NRG24/Cognitive-State-RIng/Flex Ring PCB and Schematic/Flex Ring.kicad_sch

## KiCad design Flex Ring PCB and Schematic/Flex Ring.kicad_sch (2025-12-12)

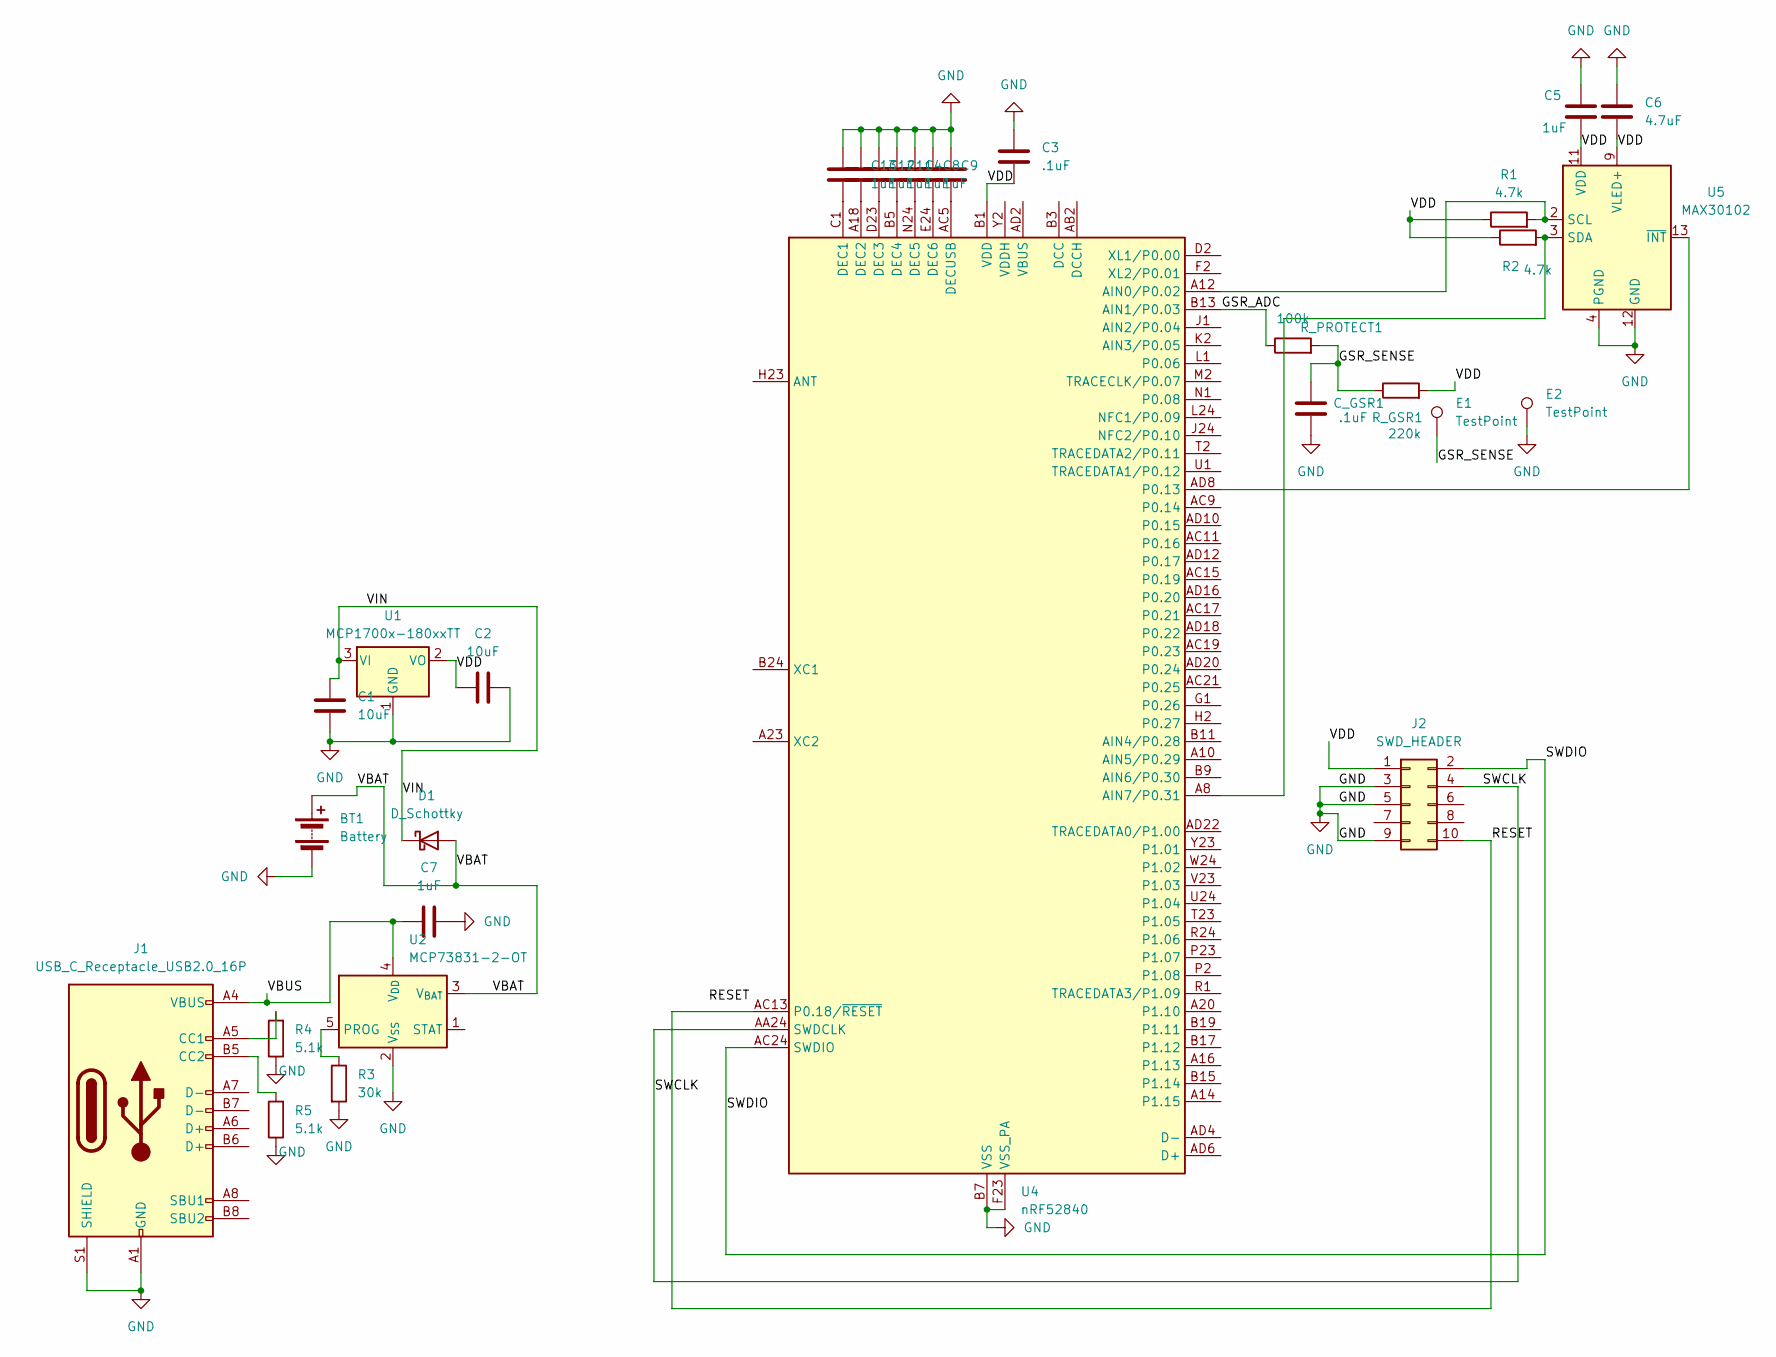
[picture p6: schematic Flex Ring.kicad_sch]

Parts:
BT1: Battery; SolderWire-0.127sqmm_1x02_P3.7mm_D0.48mm_OD1mm
C1, C2: 10uF; C_0603_1608Metric
C3: .1uF; C_0603_1608Metric
C4, C5, C7, C8, C9, C10, C11, C12, C13: 1uF; C_0603_1608Metric
C6: 4.7uF; C_0805_2012Metric
C_GSR1: .1uF; C_0603_1608Metric
D1: D_Schottky; D_SOD-123
E1: TestPoint; TestPoint_Pad_D2.0mm
E2: TestPoint; SolderWire-0.1sqmm_1x01_D0.4mm_OD1mm
J1: USB_C_Receptacle_USB2.0_16P; USB_C_Receptacle_HRO_TYPE-C-31-M-12
J2: SWD_HEADER; PinHeader_2x05_P1.27mm_Vertical
R1, R2: 4.7k; R_0603_1608Metric
R3: 30k; R_0603_1608Metric
R4, R5: 5.1k; R_0603_1608Metric
R_GSR1: 220k; R_0603_1608Metric
R_PROTECT1: 100k; R_0603_1608Metric
U1: MCP1700x-180xxTT; SOT-23
U2: MCP73831-2-OT; SOT-23-5
U4: nRF52840; Nordic_AQFN-73-1EP_7x7mm_P0.5mm
U5: MAX30102; Maxim_OLGA-14_3.3x5.6mm_P0.8mm

Connections:
GND: BT1.2 (-), C1.2, C2.2, C3.1, C4.1, C5.1, C6.1, C7.2, C8.1, C9.1, C10.1, C11.1, C12.1, C13.1, C_GSR1.2, E2.1, J1.A1 (GND), J1.A12 (GND), J1.B1 (GND), J1.B12 (GND), J1.S1 (SHIELD), J2.3, J2.5, J2.9, R3.2, R4.1, R5.1, U1.1 (GND), U2.2 (V_{SS}), U4.B7 (VSS), U4.EP (VSS), U4.F23 (VSS_PA), U5.4 (PGND), U5.12 (GND)
GSR_ADC: R_PROTECT1.1, U4.B13 (AIN1/P0.03)
GSR_SENSE: C_GSR1.1, E1.1, R_GSR1.1, R_PROTECT1.2
unnamed: C4.2, U4.B5 (DEC4)
unnamed: C8.2, U4.N24 (DEC5)
unnamed: C9.2, U4.E24 (DEC6)
unnamed: C10.2, U4.AC5 (DECUSB)
unnamed: C11.2, U4.D23 (DEC3)
unnamed: C12.2, U4.A18 (DEC2)
unnamed: C13.2, U4.C1 (DEC1)
unnamed: J1.A5 (CC1), R4.2
unnamed: J1.B5 (CC2), R5.2
unnamed: R1.2, U4.A12 (AIN0/P0.02), U5.2 (SCL)
unnamed: R2.2, U4.A8 (AIN7/P0.31), U5.3 (SDA)
unnamed: R3.1, U2.5 (PROG)
unnamed: U4.AD8 (P0.13), U5.13 (~INT)
RESET: J2.10, U4.AC13 (P0.18/~RESET)
SWCLK: J2.4, U4.AA24 (SWDCLK)
SWDIO: J2.2, U4.AC24 (SWDIO)
VBAT: BT1.1 (+), D1.2 (A), U2.3 (V_{BAT})
VBUS: C7.1, J1.A4 (VBUS), J1.A9 (VBUS), J1.B4 (VBUS), J1.B9 (VBUS), U2.4 (V_{DD})
VDD: C2.1, C3.2, C5.2, C6.2, J2.1, R1.1, R2.1, R_GSR1.2, U1.2 (VO), U4.A22 (VDD), U4.AD14 (VDD), U4.AD23 (VDD), U4.B1 (VDD), U4.W1 (VDD), U5.9 (VLED+), U5.10 (VLED+), U5.11 (VDD)
VIN: C1.1, D1.1 (K), U1.3 (VI)
